BoujeeEnjinia1701/campbreak/cad/drawings/CBK-DWG-111.pdf

### BUILD PLAN SKETCH, PLAN NOT YET BUILT CampBreak · github.com/BoujeeEnjinia1701/campbreak

FRONT VIEW
Scale 1:5; looking at the front (along +Y)

TOP VIEW
Scale 1:5; looking down (along -Z)

RIGHT VIEW
Scale 1:5; looking at the right side (along -X)

440

3 300

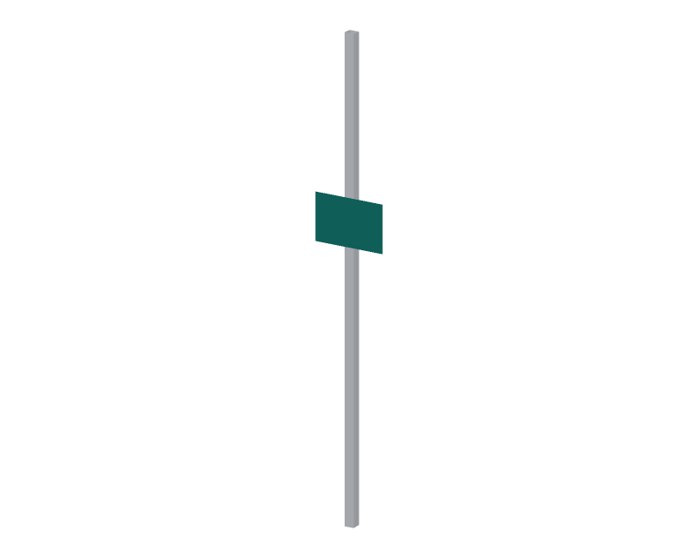
[picture p52: figure]

WHERE IT GOES
This part in colour, its neighbours in grey

HOW TO MAKE IT AND HOW IT FITS
Cut 440 x 300 mm from 3 mm aluminium; round the corners 10 mm. Two 9 mm holes on the centre line, 60 from the top and bottom edges. Print the instructions in the camp languages with pictograms:
leave first, raise the alarm, fetch the cart, small fires only,
never water on oil or live wires, call the fire service, and
go when two arrive: the first two take the cart, within 30 s. Fit: on the front face of the back right post, bottom edge 1,100 above the ground, two M8 bolts through the post.
Check: readable from 5 m in daylight.
REV | DESCRIPTION | DATE | BY
P1 | Making sketch for the prototype build plan | 2026-10-03 | AC
CAMPBREAK | github.com/BoujeeEnjinia1701/campbreak

## CampBreak station sign board: making sketch

DRAWING NO.
CBK-DWG-111

REV
P1

SHEET
1 of 1

SIZE

## ANSI B

SCALE
1:5

UNITS
mm
PROJECTION | DATE
2026-10-03

DRAWN
Amish Chadha

MATERIAL / NOTES
3 mm aluminium sheet 440 x 300 mm; printed vinyl
Licensed CERN-OHL-S-2.0 · Design Molecule Lab · designmolecule.com | Generated from cad/src; do not edit by hand
