BoujeeEnjinia1701/campbreak/cad/drawings/CBK-DWG-101.pdf

### BUILD PLAN SKETCH, PLAN NOT YET BUILT CampBreak · github.com/BoujeeEnjinia1701/campbreak

FRONT VIEW
Scale 1:10; looking at the front (along +Y)

TOP VIEW
Scale 1:10; looking down (along -Z)

RIGHT VIEW
Scale 1:10; looking at the right side (along -X)

616

1000 220

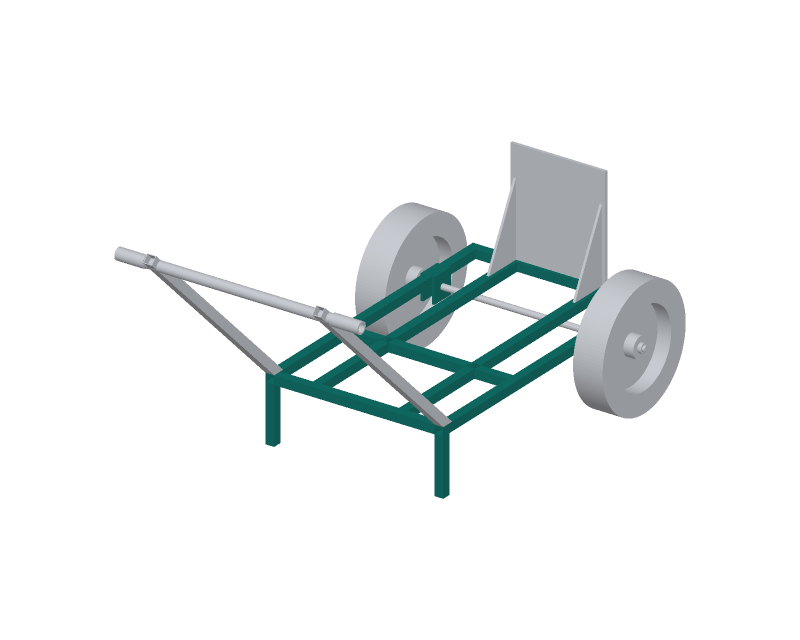
[picture p53: figure]

WHERE IT GOES
This part in colour, its neighbours in grey

HOW TO MAKE IT AND HOW IT FITS
Side rails: two tubes 1,000 long, 540 apart inside (600 outside).
Cross members, 540 long, between the rails: front, flush with the rail front ends; rear, its back face 30 in from the rail back ends; middle,
350 behind the front one, cut in three (110, 260, 110) round the bearers. Bearers: two lines of tube 260 apart inside, 320 long in front of the middle cross member and 590 behind it, all tops flush.
Legs: 190 long under each rail's front end; a 40 mm rubber foot below. Axle plates: four, 80 x 85 x 8 mm, a 21 mm hole 40 up from the bottom; one each side of each rail, centred 800 behind the rail front ends,
tops flush with the rail top. Drill the four as a stack, then weld
with a 20 mm bar through all four holes so they line up.
Weld all round on a flat table; check the diagonals before welding. Check: diagonals equal within 3 mm; the 20 mm bar turns by hand.
REV | DESCRIPTION | DATE | BY
P1 | Making sketch for the prototype build plan | 2026-10-03 | AC
CAMPBREAK | github.com/BoujeeEnjinia1701/campbreak

## CampBreak cart base frame: making sketch

DRAWING NO.
CBK-DWG-101

REV
P1

SHEET
1 of 1

SIZE

## ANSI B

SCALE
1:10

UNITS
mm
PROJECTION | DATE
2026-10-03

DRAWN
Amish Chadha

MATERIAL / NOTES
30 x 30 x 2 mm square tube and 8 mm plate, S235; MIG welded
Licensed CERN-OHL-S-2.0 · Design Molecule Lab · designmolecule.com | Generated from cad/src; do not edit by hand
