BoujeeEnjinia1701/campbreak/cad/drawings/CBK-DWG-102.pdf

### BUILD PLAN SKETCH, PLAN NOT YET BUILT CampBreak · github.com/BoujeeEnjinia1701/campbreak

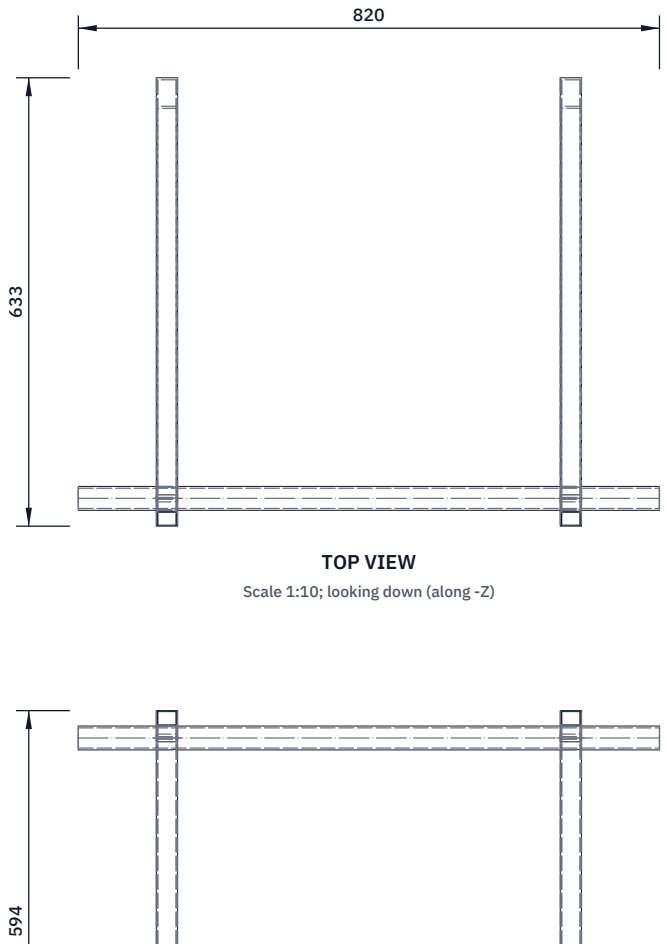
[picture p54: figure]
TOP VIEW; Scale 1:10; looking down (along -Z)
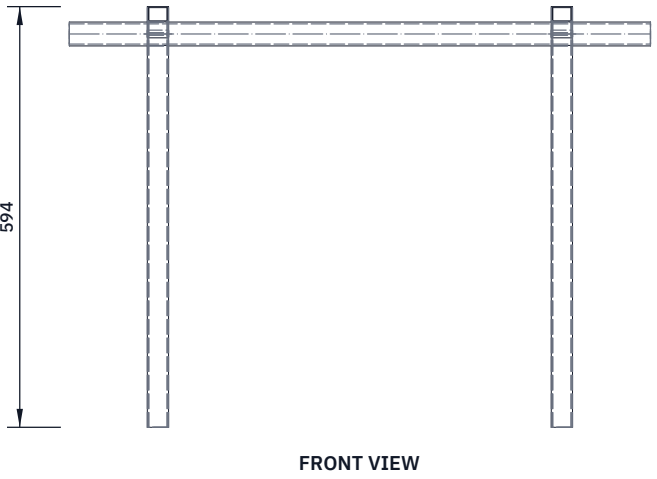
[picture p55: figure]
FRONT VIEW

Scale 1:10; looking at the front (along +Y)

RIGHT VIEW
Scale 1:10; looking at the right side (along -X)

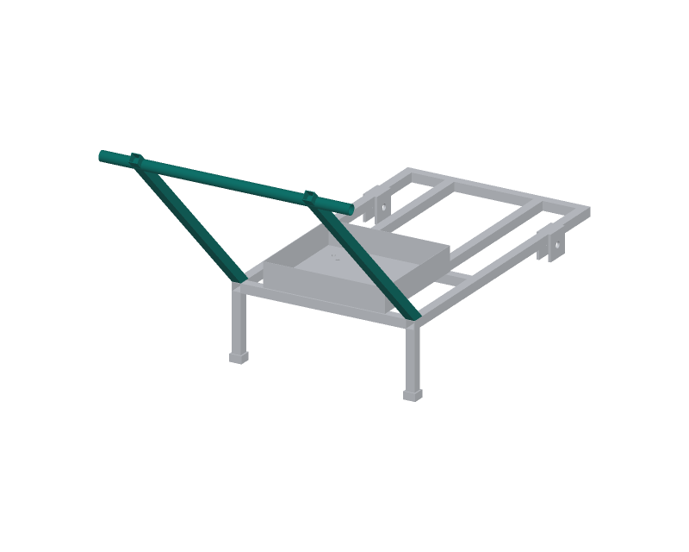
[picture p56: figure]

WHERE IT GOES
This part in colour, its neighbours in grey

HOW TO MAKE IT AND HOW IT FITS
Arms: two 30 mm tubes about 800 long, cut at 44 deg at the foot so they sit flat on the rail tops, the foot end against the front cross member. Cope the top end of each arm to the 33.7 mm bar (a saddle cut).
Cross bar: 33.7 x 2.6 mm tube 820 long, 800 above the ground and 550 in front of the rail front ends; the arms meet it 125 from each end.
Grips: 95 mm rubber grips on both bar ends, pushed on with soapy water. Tack the arms to the frame in a jig, check, then weld all round.
Check: bar level within 3 mm and square to the cart centre line.
REV | DESCRIPTION | DATE | BY
P1 | Making sketch for the prototype build plan | 2026-10-03 | AC
CAMPBREAK | github.com/BoujeeEnjinia1701/campbreak

## CampBreak pull handle (two arms and a cross bar): making sketch

DRAWING NO.
CBK-DWG-102

REV
P1

SHEET
1 of 1

SIZE

## ANSI B

SCALE
1:10

UNITS
mm
PROJECTION | DATE
2026-10-03

DRAWN
Amish Chadha

MATERIAL / NOTES
30 x 30 x 2 mm square tube; 33.7 x 2.6 mm tube; S235
Licensed CERN-OHL-S-2.0 · Design Molecule Lab · designmolecule.com | Generated from cad/src; do not edit by hand
