BoujeeEnjinia1701/campbreak/cad/drawings/CBK-DWG-103.pdf

### BUILD PLAN SKETCH, PLAN NOT YET BUILT CampBreak · github.com/BoujeeEnjinia1701/campbreak

FRONT VIEW
Scale 1:5; looking at the front (along +Y)

TOP VIEW
Scale 1:5; looking down (along -Z)

RIGHT VIEW
Scale 1:5; looking at the right side (along -X)

320

140 355

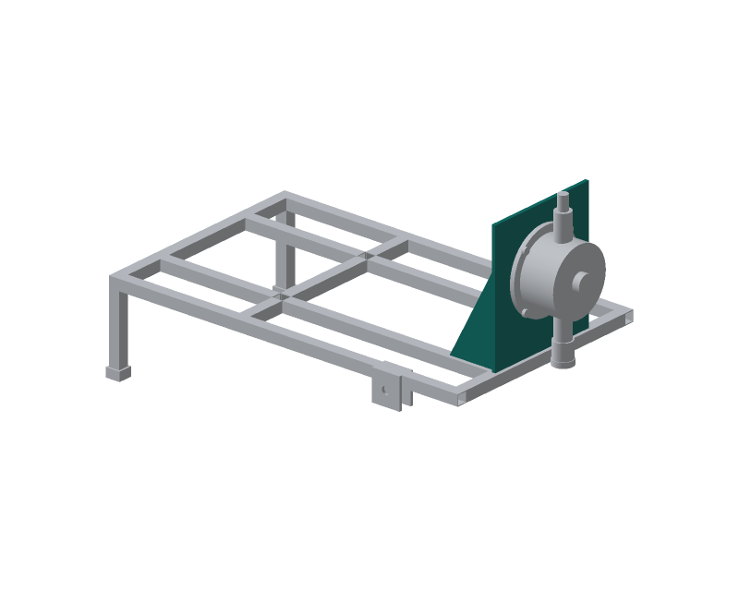
[picture p57: figure]

WHERE IT GOES
This part in colour, its neighbours in grey

HOW TO MAKE IT AND HOW IT FITS
Plate: 320 wide x 355 tall x 10 mm. Mark its centre line.
Pump holes: four 13 mm holes on a 150 mm square, centred on the centre line 195 up from the bottom edge (the pump shaft height). Check the square against the pump flange before drilling.
Gussets: two 8 mm right triangles, 130 along the bottom and 250 tall. Fit: the plate stands on the rear cross member, its front face 10 behind the member's front face, square to the bearers. The gussets sit on the bearer tops, centred on them, against the plate front.
Weld the plate to the cross member both sides; weld each gusset to the bearer and the plate.
Check: plate upright within 1 deg; holes clear of the gusset welds.
REV | DESCRIPTION | DATE | BY
P1 | Making sketch for the prototype build plan | 2026-10-03 | AC
CAMPBREAK | github.com/BoujeeEnjinia1701/campbreak

## CampBreak pump stand plate and gussets: making sketch

DRAWING NO.
CBK-DWG-103

REV
P1

SHEET
1 of 1

SIZE

## ANSI B

SCALE
1:5

UNITS
mm
PROJECTION | DATE
2026-10-03

DRAWN
Amish Chadha

MATERIAL / NOTES
10 mm plate 320 x 355 mm; two 8 mm gussets; S235
Licensed CERN-OHL-S-2.0 · Design Molecule Lab · designmolecule.com | Generated from cad/src; do not edit by hand
