BoujeeEnjinia1701/campbreak/cad/drawings/CBK-DWG-104.pdf

### BUILD PLAN SKETCH, PLAN NOT YET BUILT CampBreak · github.com/BoujeeEnjinia1701/campbreak

FRONT VIEW
Scale 1:5; looking at the front (along +Y)

TOP VIEW
Scale 1:5; looking down (along -Z)

RIGHT VIEW
Scale 1:5; looking at the right side (along -X)

260

50 365

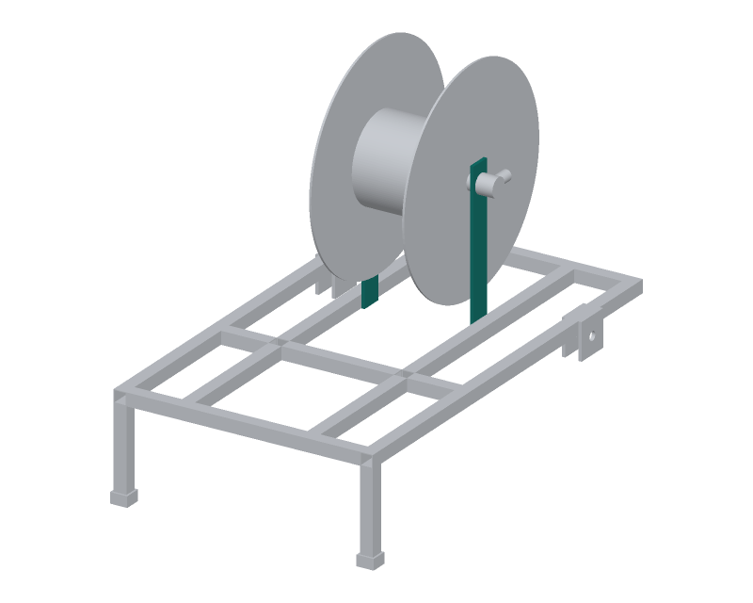
[picture p58: figure]

WHERE IT GOES
This part in colour, its neighbours in grey

HOW TO MAKE IT AND HOW IT FITS
Cut two flat bars 50 x 8 mm, 365 long, square ends.
Hole: 26 mm, centred on the bar width, 320 up from the bottom end. Drill the two bars clamped together so the holes line up.
Fit: each bar stands against the inside face of a bearer, its bottom end flush with the bearer bottom, its centre 130 in front of the
axle centre line (back edge 275 in front of the rear cross member). Weld along both edges where it touches the bearer.
Check: a 25 mm bar slides through both holes at once and is level.
REV | DESCRIPTION | DATE | BY
P1 | Making sketch for the prototype build plan | 2026-10-03 | AC
CAMPBREAK | github.com/BoujeeEnjinia1701/campbreak

## CampBreak reel uprights (make 2): making sketch

DRAWING NO.
CBK-DWG-104

REV
P1

SHEET
1 of 1

SIZE

## ANSI B

SCALE
1:5

UNITS
mm
PROJECTION | DATE
2026-10-03

DRAWN
Amish Chadha

MATERIAL / NOTES
50 x 8 mm flat bar 365 mm long; S235
Licensed CERN-OHL-S-2.0 · Design Molecule Lab · designmolecule.com | Generated from cad/src; do not edit by hand
