BoujeeEnjinia1701/campbreak/cad/drawings/CBK-DWG-105.pdf

### BUILD PLAN SKETCH, PLAN NOT YET BUILT CampBreak · github.com/BoujeeEnjinia1701/campbreak

FRONT VIEW
Scale 1:5; looking at the front (along +Y)

TOP VIEW
Scale 1:5; looking down (along -Z)

RIGHT VIEW
Scale 1:5; looking at the right side (along -X)

834

32 32

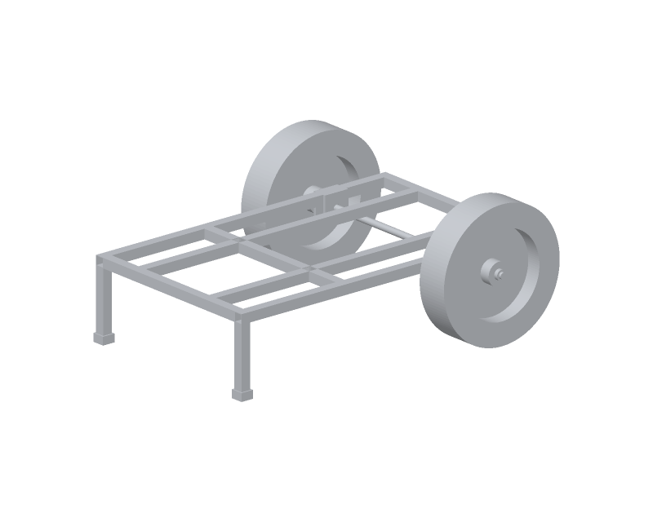
[picture p59: figure]

WHERE IT GOES
This part in colour, its neighbours in grey

HOW TO MAKE IT AND HOW IT FITS
Axle: 20 mm bright steel bar, 850 long, ends chamfered 1 mm. Drill a 4 mm cross hole 6 from each end for the R-clips.
Spacers: two 32 x 22 mm tube pieces, 22 long, ends square and deburred; they sit between the outer axle plate and the wheel hub. Collars: two 20 mm shaft collars with set screws, 12 wide, against the outside of each hub.
Order on each side, from the middle out: inner plate, rail, outer plate, spacer, wheel hub (75 long), collar, R-clip.
Check: with both wheels on, the axle end float is 1 to 2 mm.
REV | DESCRIPTION | DATE | BY
P1 | Making sketch for the prototype build plan | 2026-10-03 | AC
CAMPBREAK | github.com/BoujeeEnjinia1701/campbreak

## CampBreak axle, wheel spacers and collars: making sketch

DRAWING NO.
CBK-DWG-105

REV
P1

SHEET
1 of 1

SIZE

## ANSI B

SCALE
1:5

UNITS
mm
PROJECTION | DATE
2026-10-03

DRAWN
Amish Chadha

MATERIAL / NOTES
20 mm bright steel bar; 32 x 22 mm tube; bought collars
Licensed CERN-OHL-S-2.0 · Design Molecule Lab · designmolecule.com | Generated from cad/src; do not edit by hand
