BoujeeEnjinia1701/campbreak/cad/drawings/CBK-DWG-106.pdf

### BUILD PLAN SKETCH, PLAN NOT YET BUILT CampBreak · github.com/BoujeeEnjinia1701/campbreak

FRONT VIEW
Scale 1:2; looking at the front (along +Y)

TOP VIEW
Scale 1:2; looking down (along -Z)

RIGHT VIEW
Scale 1:2; looking at the right side (along -X)

244

40 40

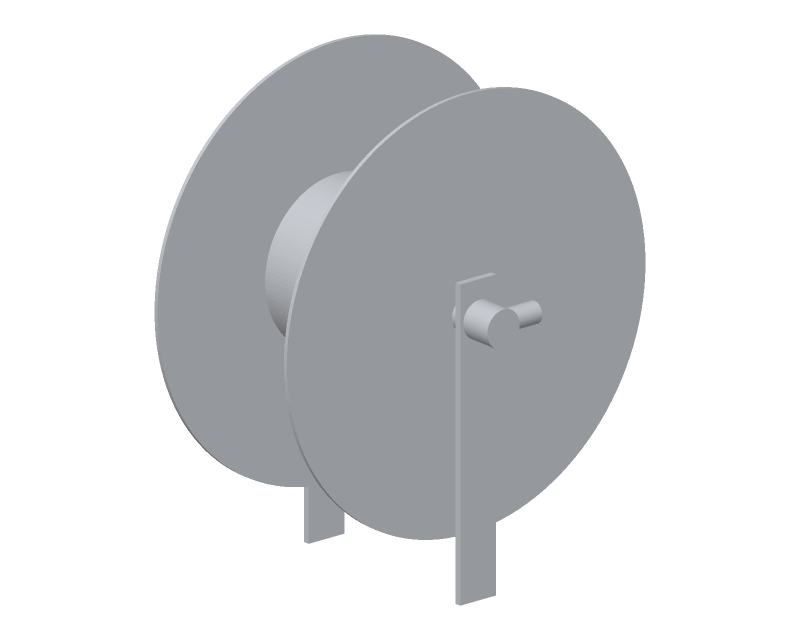
[picture p60: figure]

WHERE IT GOES
This part in colour, its neighbours in grey

HOW TO MAKE IT AND HOW IT FITS
Spindle: 25 mm bright steel bar, 290 long, ends chamfered 1 mm. Spacers: two 40 x 26 mm tube pieces, 12 long; one each side of the drum, between the drum flange boss and the upright.
Collar: a 25 mm collar with a set screw against the outside of the left upright; the swivel inlet holds the right-hand end.
Fit: the spindle passes through the left upright, a spacer, the drum, the other spacer and the right upright into the swivel.
Check: the drum turns by hand with 1 to 2 mm of side float.
REV | DESCRIPTION | DATE | BY
P1 | Making sketch for the prototype build plan | 2026-10-03 | AC
CAMPBREAK | github.com/BoujeeEnjinia1701/campbreak

## CampBreak reel spindle and spacers: making sketch

DRAWING NO.
CBK-DWG-106

REV
P1

SHEET
1 of 1

SIZE

## ANSI B

SCALE
1:2

UNITS
mm
PROJECTION | DATE
2026-10-03

DRAWN
Amish Chadha

MATERIAL / NOTES
25 mm bright steel bar; 40 x 26 mm tube; bought collar
Licensed CERN-OHL-S-2.0 · Design Molecule Lab · designmolecule.com | Generated from cad/src; do not edit by hand
