BoujeeEnjinia1701/campbreak/cad/drawings/CBK-DWG-107.pdf

### BUILD PLAN SKETCH, PLAN NOT YET BUILT CampBreak · github.com/BoujeeEnjinia1701/campbreak

FRONT VIEW
Scale 1:10; looking at the front (along +Y)

TOP VIEW
Scale 1:10; looking down (along -Z)

RIGHT VIEW
Scale 1:10; looking at the right side (along -X)

400

38 648

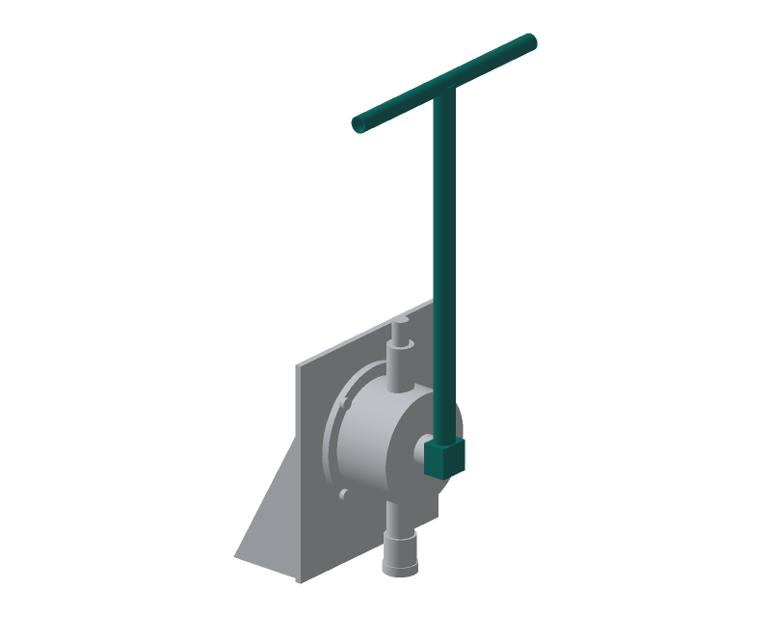
[picture p61: figure]

WHERE IT GOES
This part in colour, its neighbours in grey

HOW TO MAKE IT AND HOW IT FITS
Hub: 50 x 50 mm block, 38 thick, bored and slotted to clamp on the pump's handle socket with two M10 bolts (fit it to the pump bought). Lever: 33.7 x 2.6 mm tube 585 long, welded on top of the hub.
T-bar: 27 x 2.3 mm tube 400 long, welded across the lever top, square to the pump shaft, 610 above the shaft centre.
Grips: 100 mm rubber grips on both T-bar ends.
Fit: the lever stands upright at mid-stroke and swings 40 deg each way. Two people face each other across the T-bar.
Check: at both ends of the swing the grip is at least 50 from the wheels and 30 from the frame.
REV | DESCRIPTION | DATE | BY
P1 | Making sketch for the prototype build plan | 2026-10-03 | AC
CAMPBREAK | github.com/BoujeeEnjinia1701/campbreak

## CampBreak lever extension with T-grip: making sketch

DRAWING NO.
CBK-DWG-107

REV
P1

SHEET
1 of 1

SIZE

## ANSI B

SCALE
1:10

UNITS
mm
PROJECTION | DATE
2026-10-03

DRAWN
Amish Chadha

MATERIAL / NOTES
33.7 x 2.6 and 27 x 2.3 mm tube; 50 mm square bar hub; S235
Licensed CERN-OHL-S-2.0 · Design Molecule Lab · designmolecule.com | Generated from cad/src; do not edit by hand
