BoujeeEnjinia1701/campbreak/cad/drawings/CBK-DWG-108.pdf

### BUILD PLAN SKETCH, PLAN NOT YET BUILT CampBreak · github.com/BoujeeEnjinia1701/campbreak

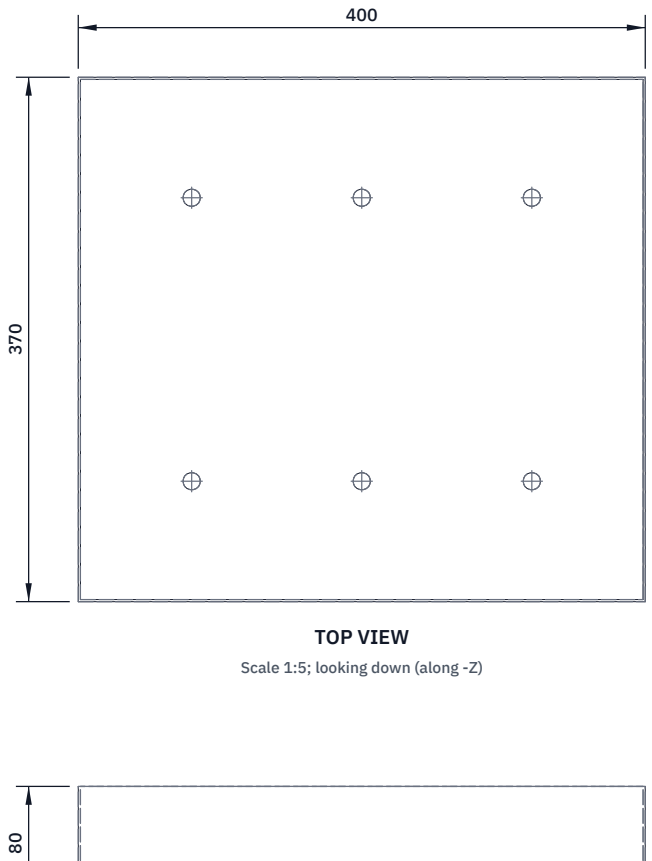
[picture p62: figure]
TOP VIEW; Scale 1:5; looking down (along -Z)

FRONT VIEW
Scale 1:5; looking at the front (along +Y)

RIGHT VIEW
Scale 1:5; looking at the right side (along -X)

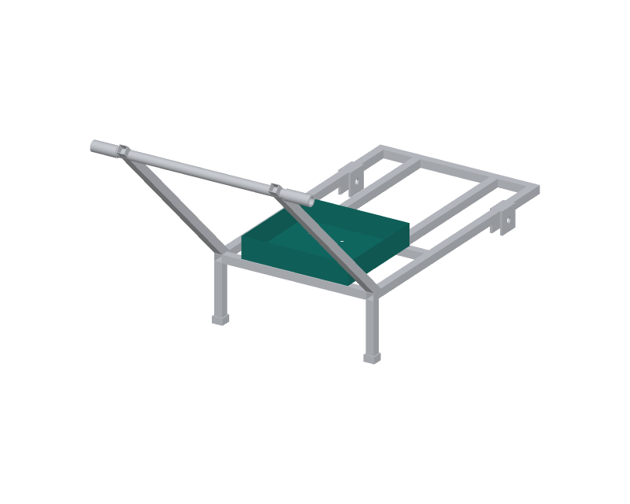
[picture p63: figure]

WHERE IT GOES
This part in colour, its neighbours in grey

HOW TO MAKE IT AND HOW IT FITS
Blank 560 x 530 mm. Cut an 80 mm square out of each corner. Holes in the floor, before folding: six 12 mm drain holes at 120 mm spacing across and 200 mm along; four 9 mm bolt holes, 145 each side of the centre line, 120 in front of and behind the middle.
Fold the four sides up 90 deg to 80 tall; tray 400 x 370 outside. Pop-rivet or spot-weld the corners; paint the cut edges.
Fit: the tray sits on the bearers and front cross member tops, centred, its front edge 5 behind the front cross member's front face; four M8 bolts through the bearer tops, nuts below. Check: the tray sits flat and clears the handle arms by 30 mm.
REV | DESCRIPTION | DATE | BY
P1 | Making sketch for the prototype build plan | 2026-10-03 | AC
CAMPBREAK | github.com/BoujeeEnjinia1701/campbreak

## CampBreak hose tray: making sketch

DRAWING NO.
CBK-DWG-108

REV
P1

SHEET
1 of 1

SIZE

## ANSI B

SCALE
1:5

UNITS
mm
PROJECTION | DATE
2026-10-03

DRAWN
Amish Chadha

MATERIAL / NOTES
1.5 mm galvanised steel sheet, blank 560 x 530 mm
Licensed CERN-OHL-S-2.0 · Design Molecule Lab · designmolecule.com | Generated from cad/src; do not edit by hand
