BoujeeEnjinia1701/campbreak/cad/drawings/CBK-DWG-109.pdf

### BUILD PLAN SKETCH, PLAN NOT YET BUILT CampBreak · github.com/BoujeeEnjinia1701/campbreak

FRONT VIEW
Scale 1:50; looking at the front (along +Y)

TOP VIEW
Scale 1:50; looking down (along -Z)

RIGHT VIEW
Scale 1:50; looking at the right side (along -X)

300

2100 3160

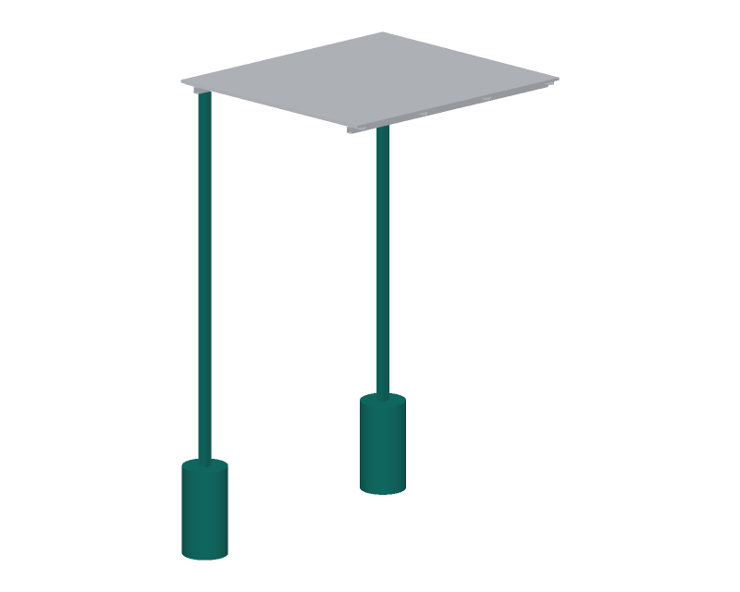
[picture p64: figure]

WHERE IT GOES
This part in colour, its neighbours in grey

HOW TO MAKE IT AND HOW IT FITS
Four posts: two front (3,160 long) and two back (3,000 long), each set 600 into the ground; the tops are cut at 5 deg so the roof
falls to the back. Back posts stand 2,400 above the ground.
Layout: 1,300 between post centres across, 1,800 front to back. Holes: two 13 mm holes across each post top, 60 down, for the beam cleats; 9 mm holes for the box, siren and sign brackets on site.
Paint the buried 700 mm with bitumen; cap the tops.
Collars: auger 300 mm holes 650 deep; 50 mm of gravel; stand the post plumb on it and pour concrete to ground level, sloped to shed water. Check: posts plumb within 5 mm over 2 m; diagonals equal within 10.
REV | DESCRIPTION | DATE | BY
P1 | Making sketch for the prototype build plan | 2026-10-03 | AC
CAMPBREAK | github.com/BoujeeEnjinia1701/campbreak

## CampBreak station posts and concrete collars (left pair drawn): making sketch

DRAWING NO.
CBK-DWG-109

REV
P1

SHEET
1 of 1

SIZE

## ANSI B

SCALE
1:50

UNITS
mm
PROJECTION | DATE
2026-10-03

DRAWN
Amish Chadha

MATERIAL / NOTES
60 x 60 x 3 mm square tube, S235; concrete collars 300 mm across
Licensed CERN-OHL-S-2.0 · Design Molecule Lab · designmolecule.com | Generated from cad/src; do not edit by hand
