BoujeeEnjinia1701/campbreak/cad/drawings/CBK-DWG-110.pdf

### BUILD PLAN SKETCH, PLAN NOT YET BUILT CampBreak · github.com/BoujeeEnjinia1701/campbreak

FRONT VIEW
Scale 1:20; looking at the front (along +Y)

TOP VIEW
Scale 1:20; looking down (along -Z)

RIGHT VIEW
Scale 1:20; looking at the right side (along -X)

1500

1996 233

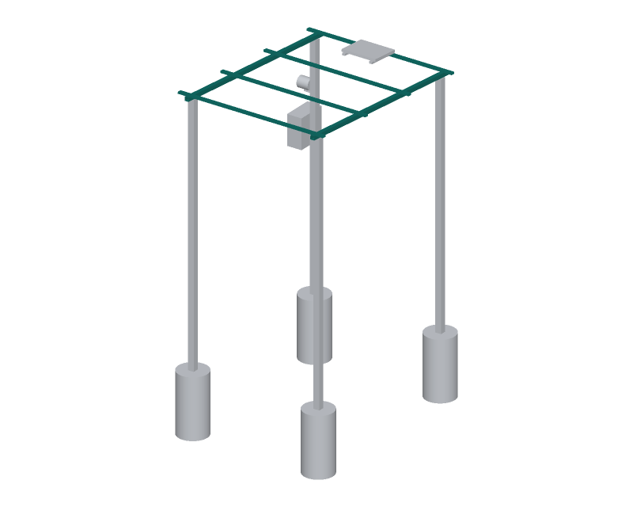
[picture p65: figure]

WHERE IT GOES
This part in colour, its neighbours in grey

HOW TO MAKE IT AND HOW IT FITS
Beams: two 40 x 40 x 2 tubes 2,000 long, one over each pair of posts, reaching 100 past the front and the back post centres.
Fix each beam to its post tops with a 40 x 40 x 4 angle cleat and
two M8 bolts, or weld it on site.
Purlins: four 40 x 20 x 2 tubes 1,500 long across the beams, at
30, 660, 1,300 and 1,940 from the beams' front ends; weld or bolt with an M8 bolt through each crossing.
Roof sheet: corrugated galvanised 1,500 x 2,050, fixed to each purlin with roofing screws and washers on every second crest.
Check: the roof falls 5 deg to the back; no sheet edge overhangs a path by more than 100.
REV | DESCRIPTION | DATE | BY
P1 | Making sketch for the prototype build plan | 2026-10-03 | AC
CAMPBREAK | github.com/BoujeeEnjinia1701/campbreak

## CampBreak roof beams and purlins: making sketch

DRAWING NO.
CBK-DWG-110

REV
P1

SHEET
1 of 1

SIZE

## ANSI B

SCALE
1:20

UNITS
mm
PROJECTION | DATE
2026-10-03

DRAWN
Amish Chadha

MATERIAL / NOTES
40 x 40 x 2 and 40 x 20 x 2 mm tube; S235
Licensed CERN-OHL-S-2.0 · Design Molecule Lab · designmolecule.com | Generated from cad/src; do not edit by hand
