BoujeeEnjinia1701/campbreak/cad/drawings/CBK-DWG-112.pdf

### BUILD PLAN SKETCH, PLAN NOT YET BUILT CampBreak · github.com/BoujeeEnjinia1701/campbreak

FRONT VIEW
Scale 1:2; looking at the front (along +Y)

TOP VIEW
Scale 1:2; looking down (along -Z)

RIGHT VIEW
Scale 1:2; looking at the right side (along -X)

140

100 57

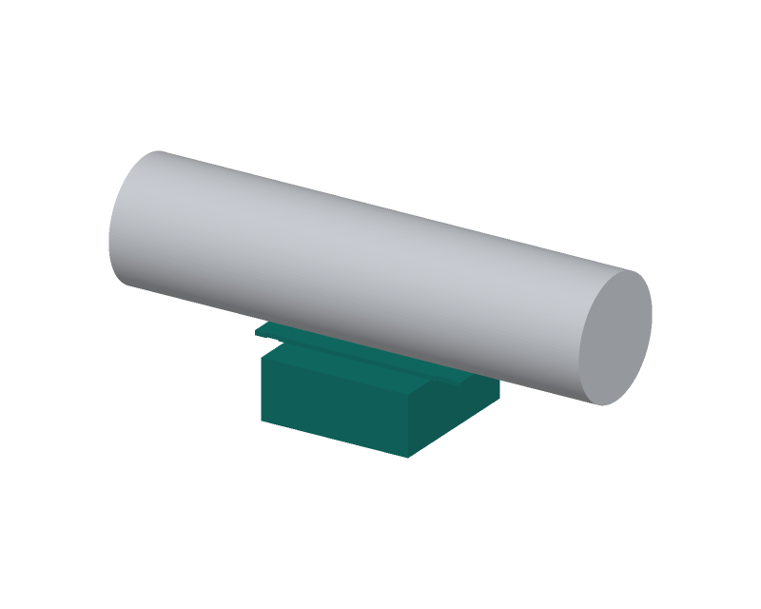
[picture p66: figure]

WHERE IT GOES
This part in colour, its neighbours in grey

HOW TO MAKE IT AND HOW IT FITS
Plate: 140 x 50 x 3 mm aluminium. Four slots 8 x 3 mm, 58 each side of the middle, 24 to 27 from the long centre line, for the ties.
Two 4.5 mm holes 30 each side of the middle for M4 screws.
Box base (22 deep): two 3.3 mm holes to match the plate; screw the plate on from inside with two M4 screws.
Box cover (18 deep): a 12 mm hole in the middle for the thermistor; eight 5 mm sound holes round a point 25 from the middle.
Guard: printed PETG cup 24 across, 14 tall, six side slots; glued over the 12 mm hole so the bead sits in moving air.
Fit: plate flat under a roof pole, held by two UV-stable ties. Check: the cover closes on its seal with the board inside.
REV | DESCRIPTION | DATE | BY
P1 | Making sketch for the prototype build plan | 2026-10-03 | AC
CAMPBREAK | github.com/BoujeeEnjinia1701/campbreak

## CampBreak heat alarm mounting plate, box and sensor guard: making sketch

DRAWING NO.
CBK-DWG-112

REV
P1

SHEET
1 of 1

SIZE

## ANSI B

SCALE
1:2

UNITS
mm
PROJECTION | DATE
2026-10-03

DRAWN
Amish Chadha

MATERIAL / NOTES
3 mm aluminium plate; stock ABS box 100 x 100 x 40; printed PETG guard
Licensed CERN-OHL-S-2.0 · Design Molecule Lab · designmolecule.com | Generated from cad/src; do not edit by hand
