BoujeeEnjinia1701/campbreak/cad/drawings/CBK-DWG-001.png

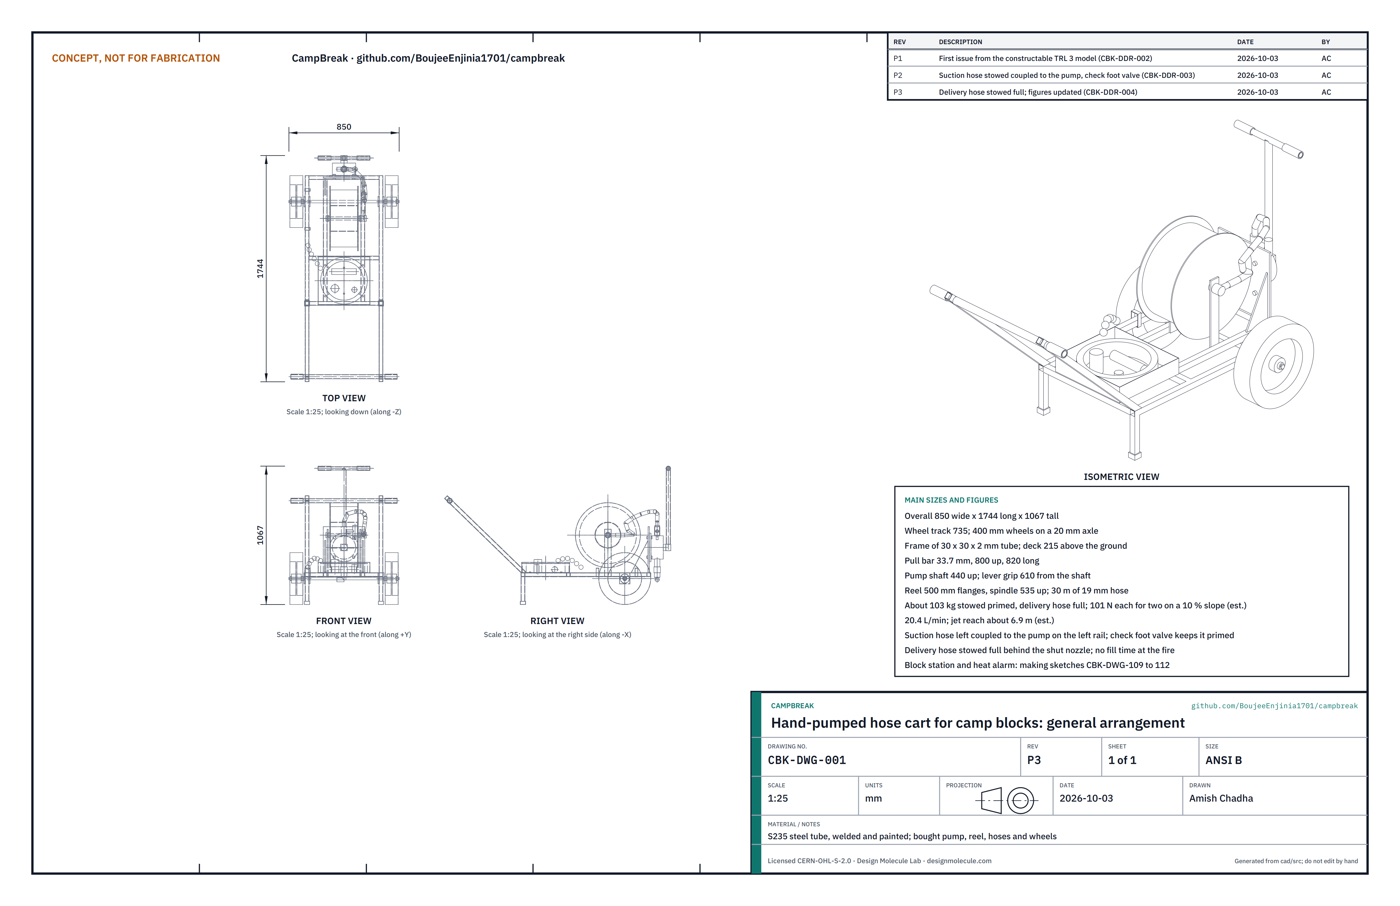
cad/drawings/CBK-DWG-001.png
