BoujeeEnjinia1701/campbreak/media/card.png

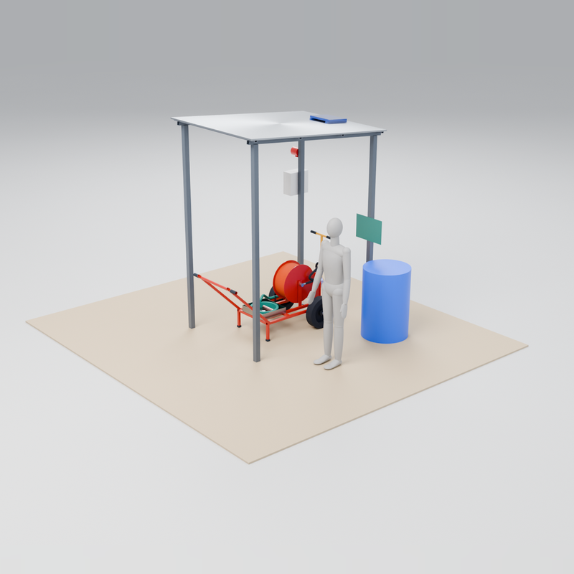
media/card.png
