BoujeeEnjinia1701/campbreak/media/concept-blueprint.png

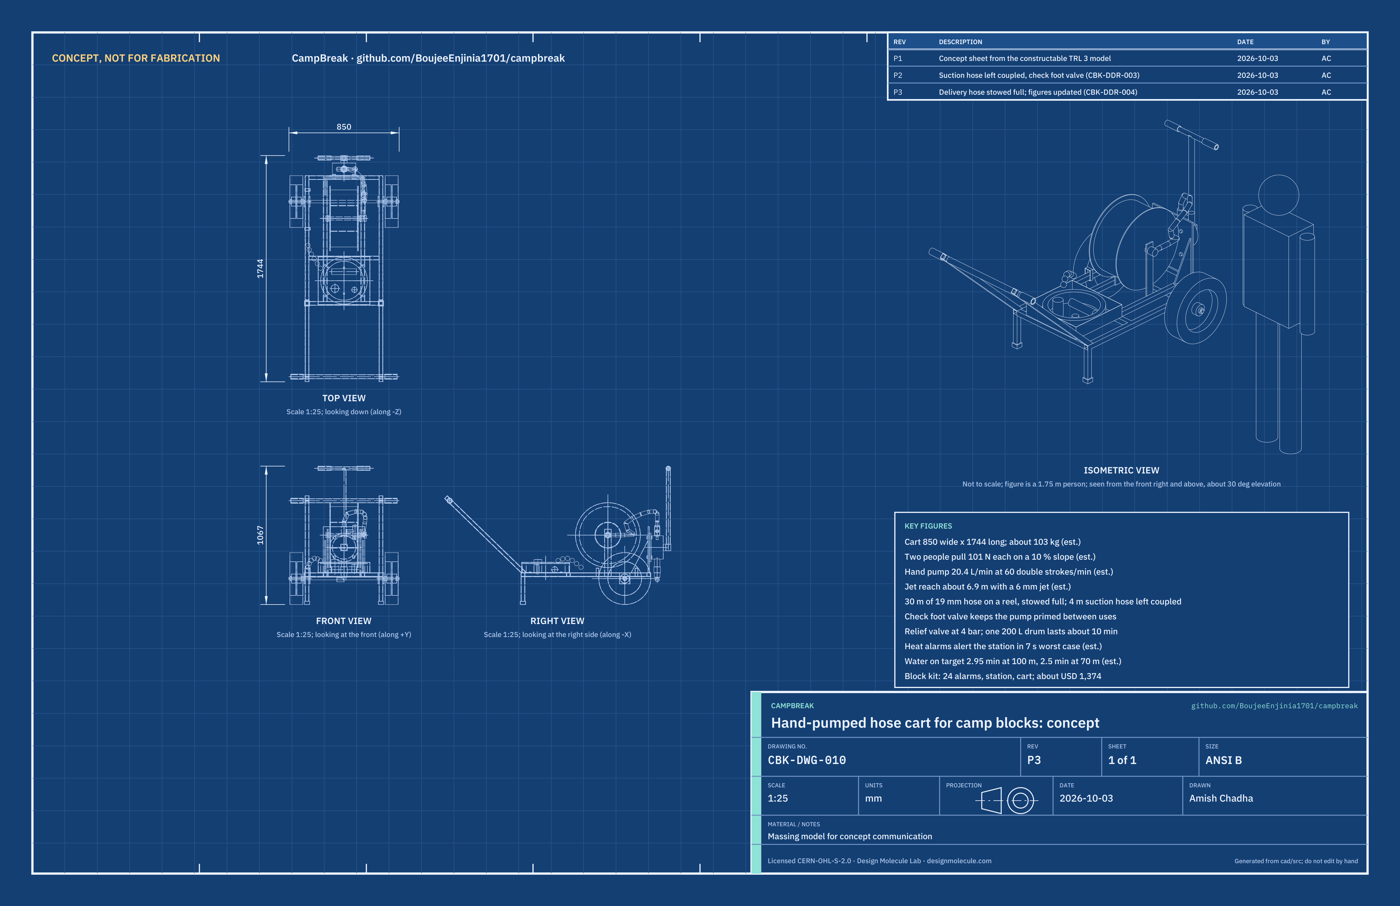
media/concept-blueprint.png
