BoujeeEnjinia1701/campbreak/media/render-detail.png

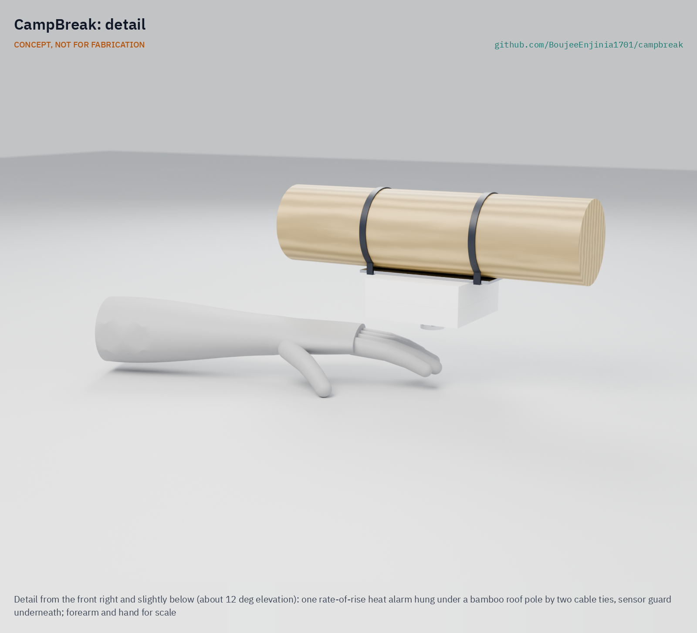
media/render-detail.png
