BoujeeEnjinia1701/campbreak/media/render-exploded.png

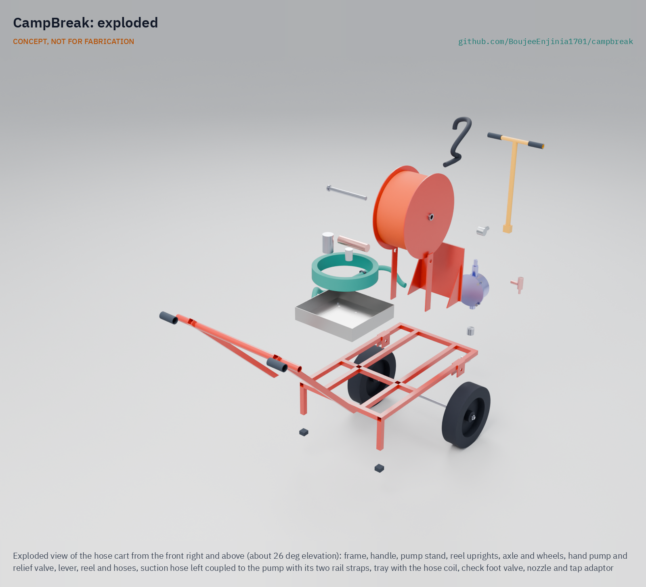
media/render-exploded.png
