BoujeeEnjinia1701/campbreak/media/social-preview.png

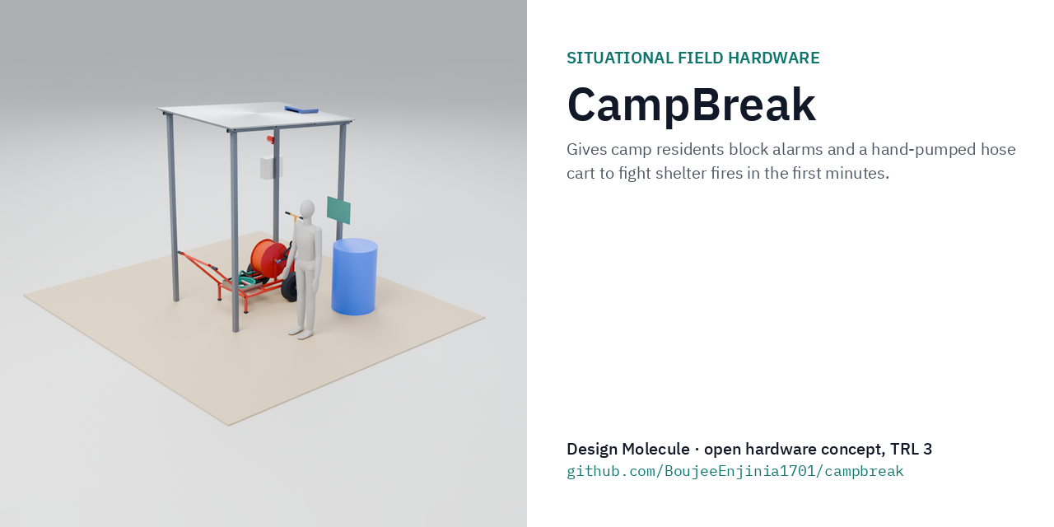
media/social-preview.png
